samraatpchauhan-eng/Airbus-FCU-Macropad/Assets/Airbus-FCU-Case_2026-Jul-02_07-27-54PM-000_CustomizedView25010296873.png

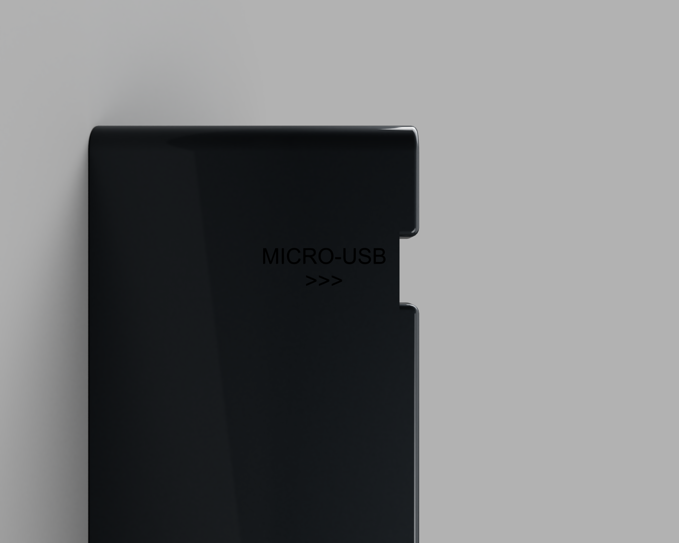
Assets/Airbus-FCU-Case_2026-Jul-02_07-27-54PM-000_CustomizedView25010296873.png
