samraatpchauhan-eng/Airbus-FCU-Macropad/Assets/Airbus-FCU-Case_2026-Jul-02_07-30-18PM-000_CustomizedView15151844348.png

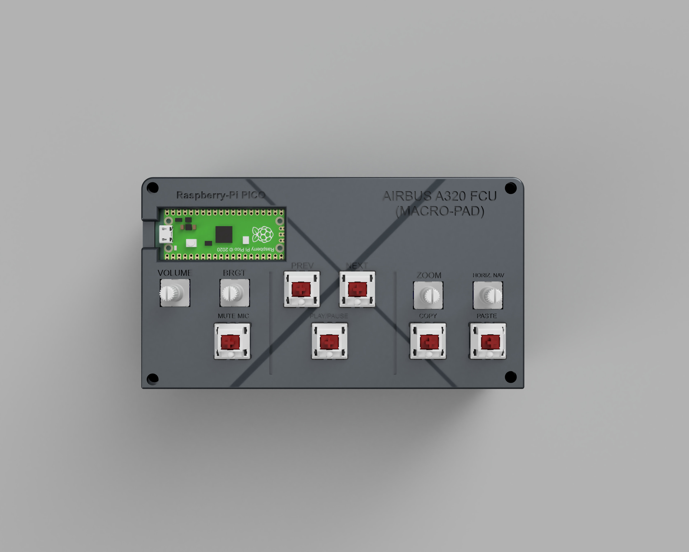
Assets/Airbus-FCU-Case_2026-Jul-02_07-30-18PM-000_CustomizedView15151844348.png
