samraatpchauhan-eng/Airbus-FCU-Macropad/Assets/Airbus-FCU-Case_2026-Jul-02_07-37-07PM-000_CustomizedView3551822146.png

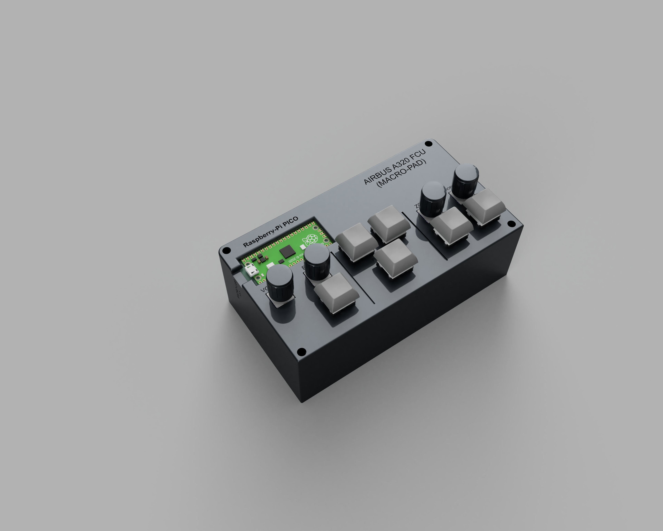
Assets/Airbus-FCU-Case_2026-Jul-02_07-37-07PM-000_CustomizedView3551822146.png
