samraatpchauhan-eng/Airbus-FCU-Macropad/Assets/Screenshot 2026-07-01 002943.png

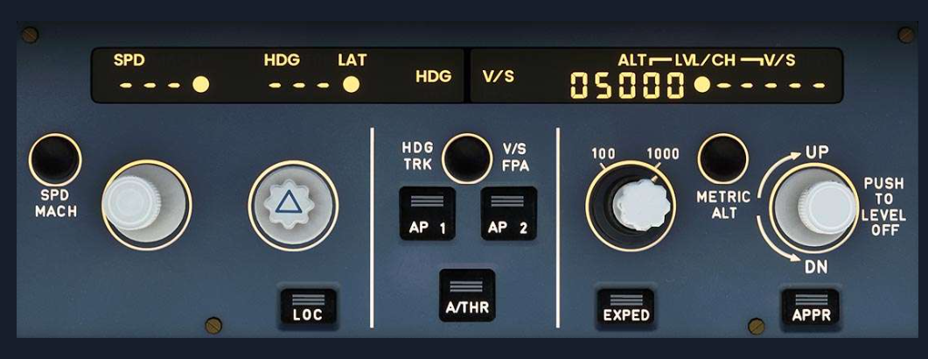
Assets/Screenshot 2026-07-01 002943.png
