samraatpchauhan-eng/Airbus-FCU-Macropad/Assets/Screenshot 2026-07-04 104919.png

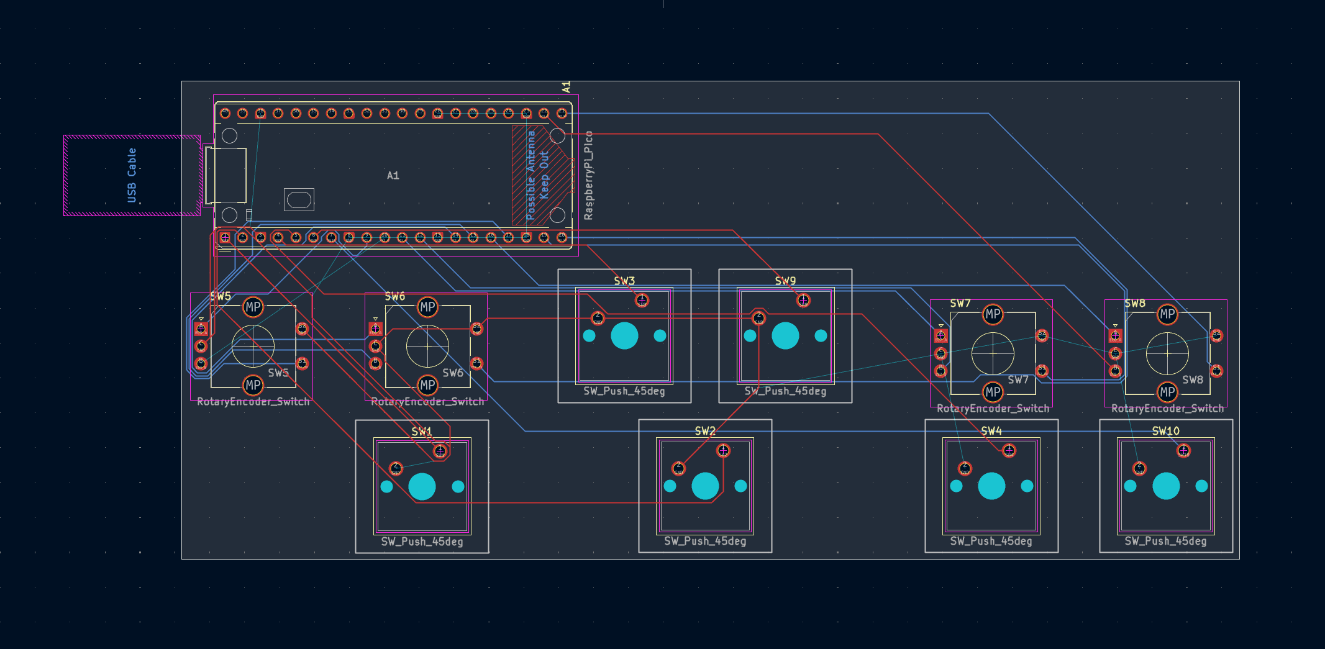
Assets/Screenshot 2026-07-04 104919.png
